tomcircuit/TI59_battery/media/holder_stl_view.PNG

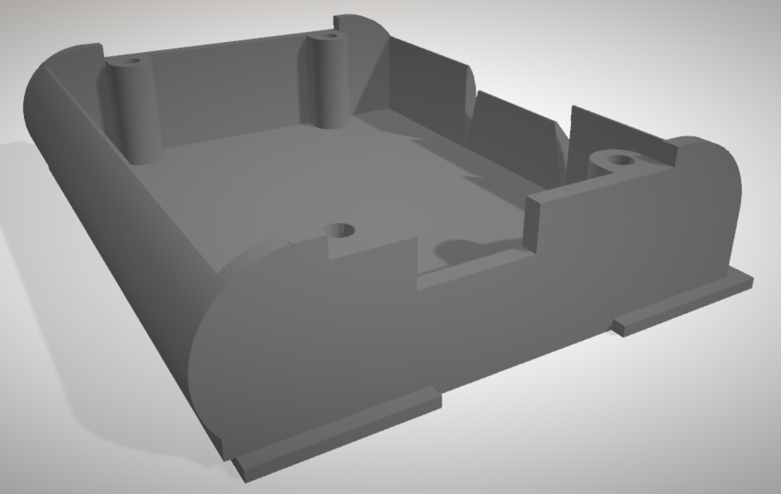
media/holder_stl_view.PNG
