tomcircuit/TI59_battery/media/scad_view.PNG

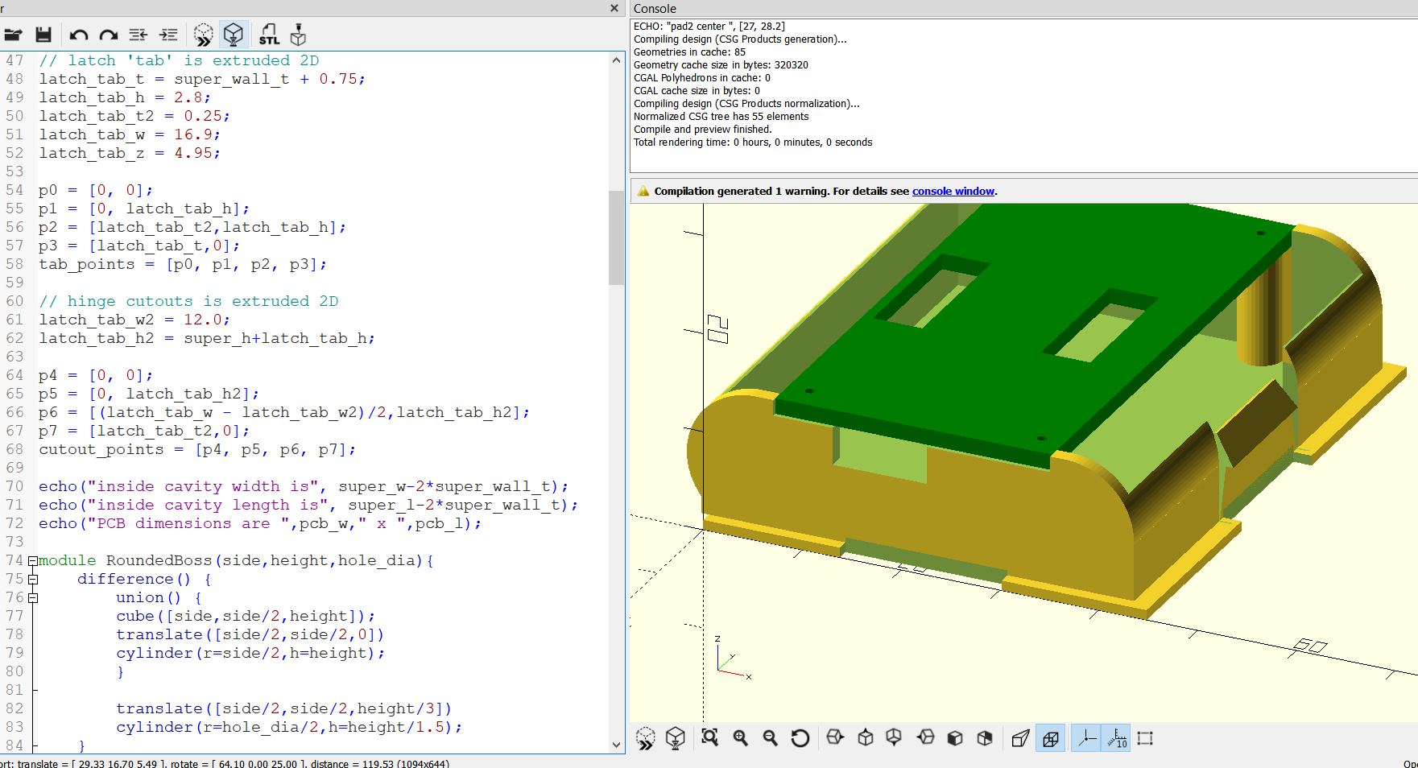
media/scad_view.PNG
