tomcircuit/TI59_battery/media/TI-59_BP1A.jpg

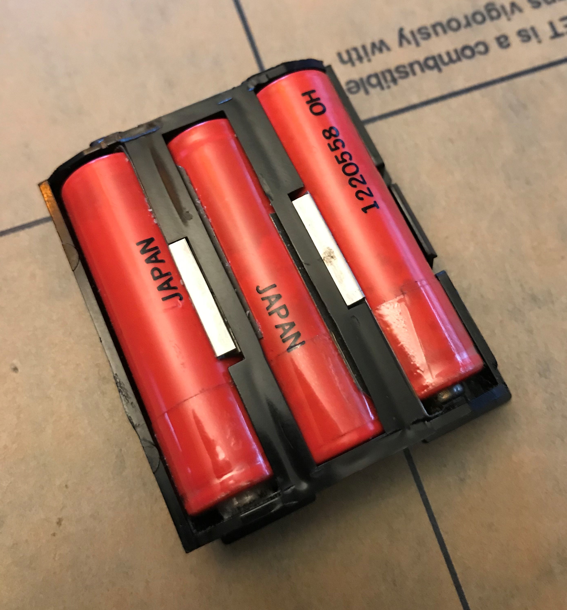
media/TI-59_BP1A.jpg
