tomcircuit/TI59_battery/media/TI-59_pack_assembled.jpg

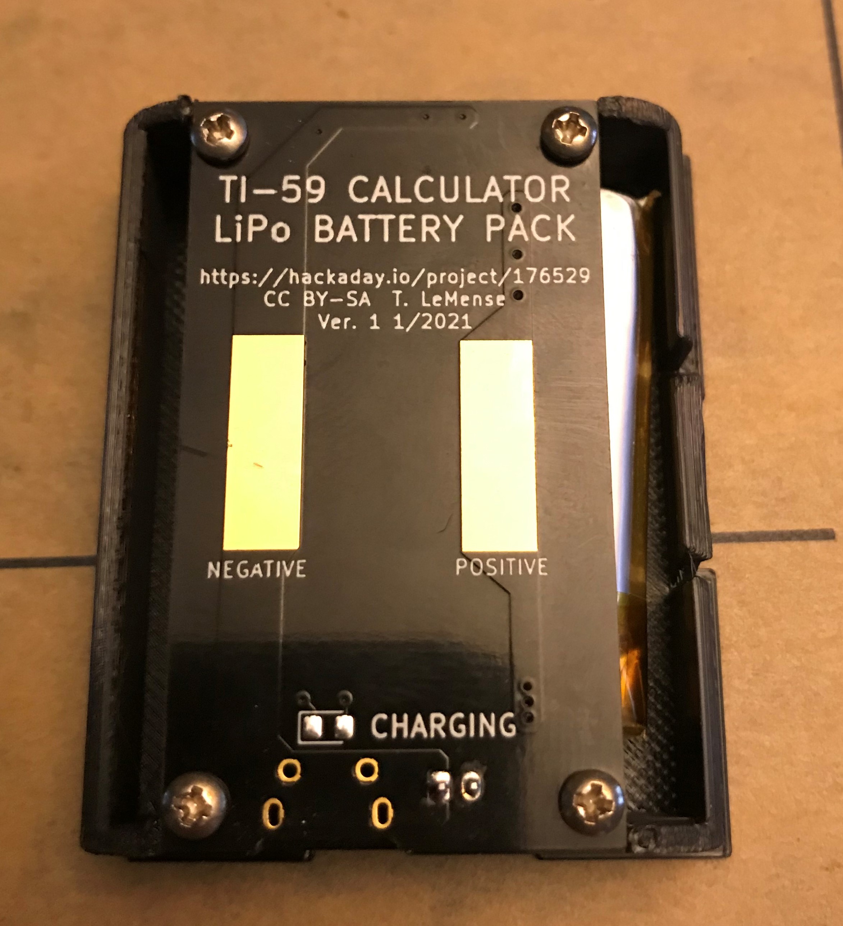
media/TI-59_pack_assembled.jpg
